codeophile/STM32Othello/Software/Inc/WS64_Data.h

/********************************************************************************
 WS64_DrawMaps.h
 ********************************************************************************/

#ifndef INC_WS64_DrawMaps_H_
#define INC_WS64_DrawMaps_H_

//Patterns for testing
uchar pattern[][8] = {
	{ 0x00, 0x3e, 0x41, 0x41, 0x41, 0x41, 0x41, 0x3e }, //letter O
	{ 0x00, 0x01, 0x01, 0x01, 0x7f, 0x01, 0x01, 0x01 }, //letter T
	};

const uchar snakeMap0[] = {
	//TOP LEFT TOWARDS BOTTOM LEFT
	0, 1, 2, 3, 4, 5, 6, 7,
	15, 14, 13, 12, 11, 10, 9, 8,
	16, 17, 18, 19, 20, 21, 22, 23,
	31, 30, 29, 28, 27, 26, 25, 24,
	32, 33, 34, 35, 36, 37, 38, 39,
	47, 46, 45, 44, 43, 42, 41, 40,
	48, 49, 50, 51, 52, 53, 54, 55,
	63, 62, 61, 60, 59, 58, 57, 56,
};

const uchar snakeMap1[] = {
	//TOP LEFT CW TO LOWER LEFT CENTER
	0, 1, 2, 3, 4, 5, 6, 7,
	15, 23, 31, 39, 47, 55, 63,
	62, 61, 60, 59, 58, 57, 56,
	48, 40, 32, 24, 16, 8,
	//2nd
	9, 10, 11, 12, 13, 14,
	22, 30, 38, 46, 54,
	53, 52, 51, 50, 49,
	41, 33, 25, 17,
	//3rd
	18, 19, 20, 21,
	29, 37, 45,
	44, 43, 42,
	34, 26,
	//4th
	27, 28, //36,35
	};
const uchar snakeMap2[] = {
	//TOP LEFT CENTER CW TO LOWER LEFT
	//4th
	27, 28, 36, 35,
	//3rd
	34, 26, 18,
	19, 20, 21,
	29, 37, 45,
	44, 43, 42, 41,
	//2nd
	33, 25, 17, 9,
	10, 11, 12, 13, 14,
	22, 30, 38, 46, 54,
	53, 52, 51, 50, 49,
	48, 40, 32, 24, 16, 8, 0,
	//1st
	1, 2, 3, 4, 5, 6, 7,
	15, 23, 31, 39, 47, 55, 63,
	62, 61, 60, 59, 58, 57, 56,
};

const uchar snakeMap3[] = {
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
	{ 0x3E, 0x41, 0x41, 0x41, 0x22 }, //C
	{ 0x7F, 0x41, 0x41, 0x22, 0x1C }, //D
	{ 0x7F, 0x49, 0x49, 0x49, 0x41 }, //E
	{ 0x7F, 0x09, 0x09, 0x09, 0x01 }, //F
	{ 0x3E, 0x41, 0x49, 0x49, 0x7A }, //G
	{ 0x7F, 0x08, 0x08, 0x08, 0x7F }, //H
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
};

#endif /* INC_WS64_DrawMaps_H_  */
